Videocraft10/Vid-USB-Hub/Promo Files/Exports/BackgroundExport.png

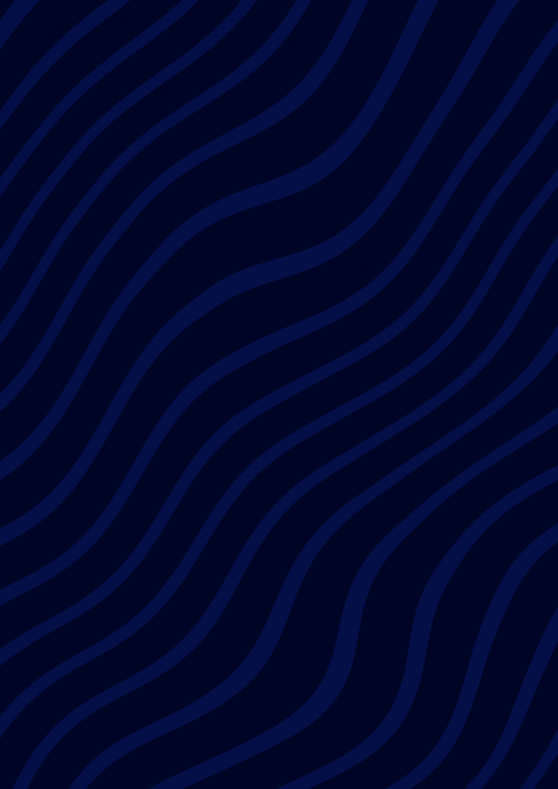
Promo Files/Exports/BackgroundExport.png
