Videocraft10/Vid-USB-Hub/Promo Files/Exports/BackgroundExportBland.png

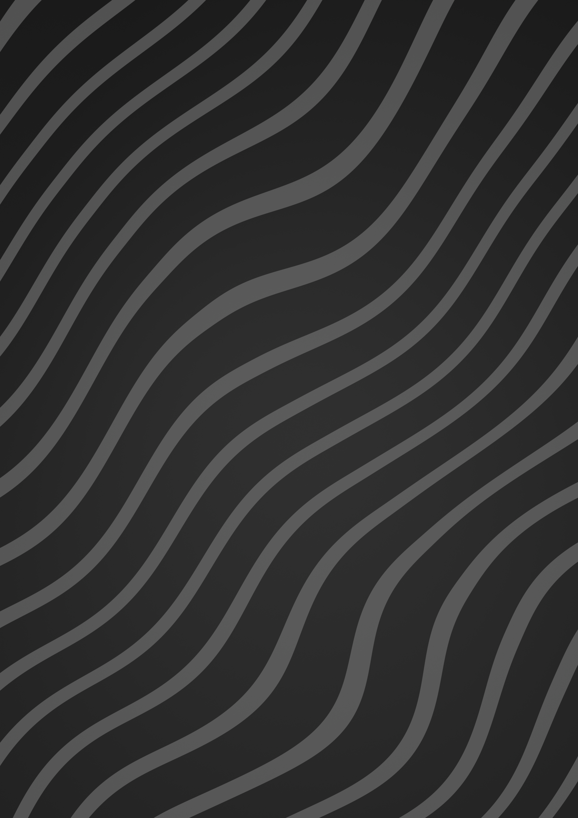
Promo Files/Exports/BackgroundExportBland.png
