Videocraft10/Vid-USB-Hub/Promo Files/Exports/BackgroundExportGlow.png

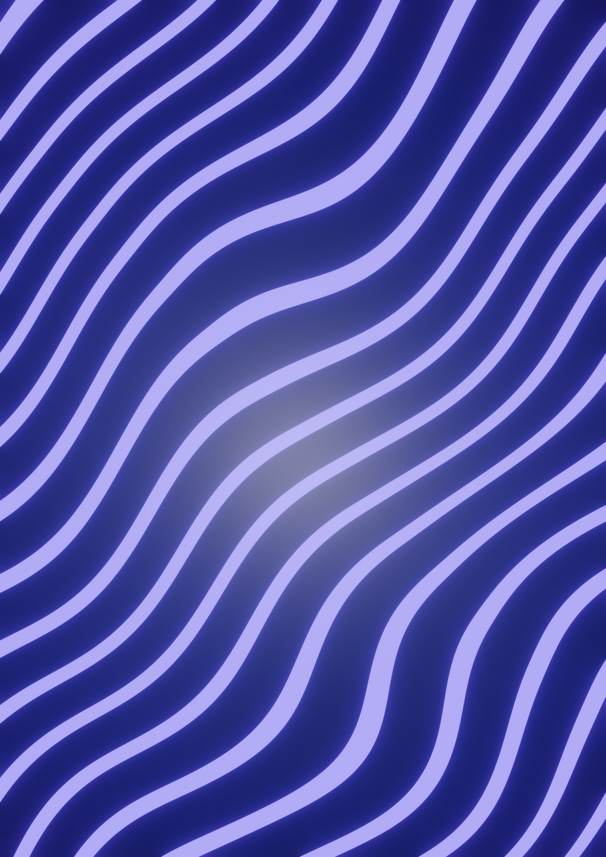
Promo Files/Exports/BackgroundExportGlow.png
