Videocraft10/Vid-USB-Hub/Promo Files/Exports/GitHubQR.png

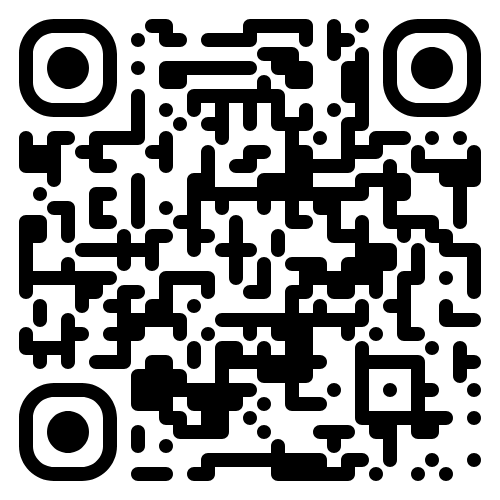
Promo Files/Exports/GitHubQR.png
