Videocraft10/Vid-USB-Hub/Promo Files/Exports/USB Grafiti Flip.png

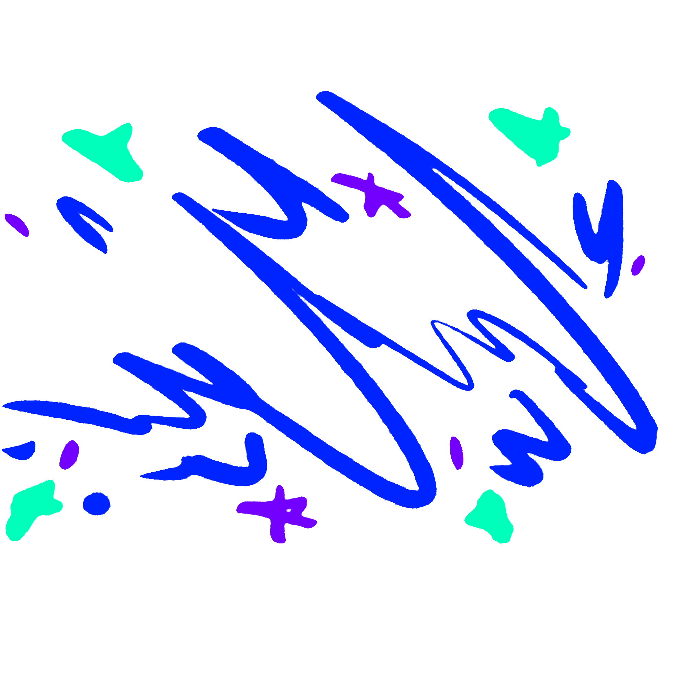
Promo Files/Exports/USB Grafiti Flip.png
