Videocraft10/Vid-USB-Hub/Promo Files/Exports/USB Grafiti Zinev2 flip.png

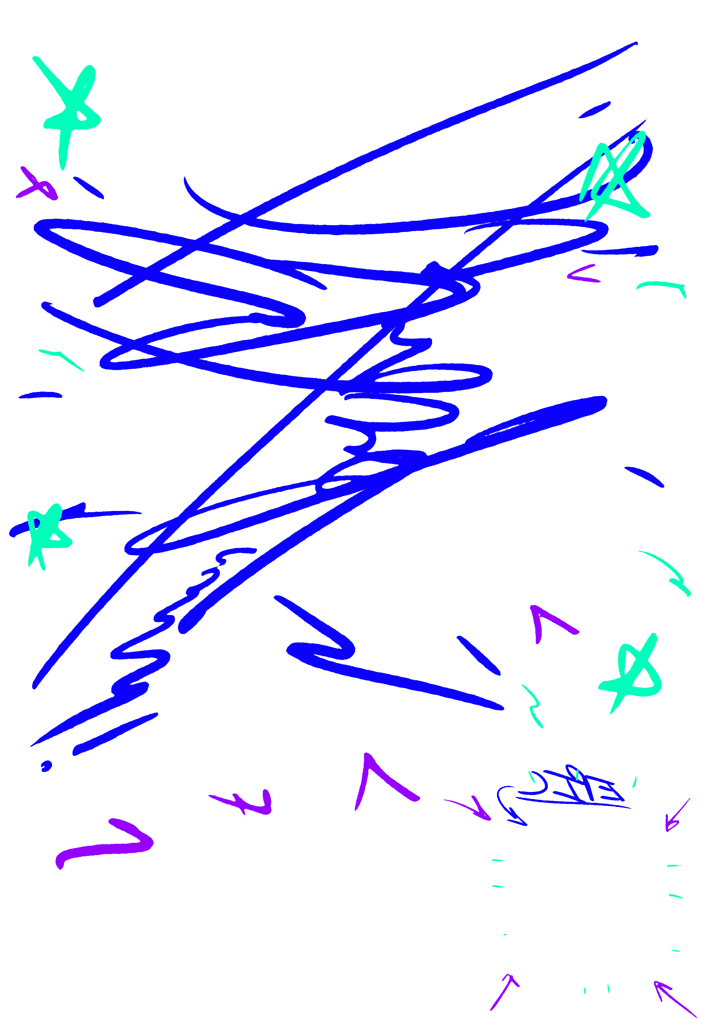
Promo Files/Exports/USB Grafiti Zinev2 flip.png
