Videocraft10/Vid-USB-Hub/Promo Files/Exports/USB Grafiti Zinev2.png

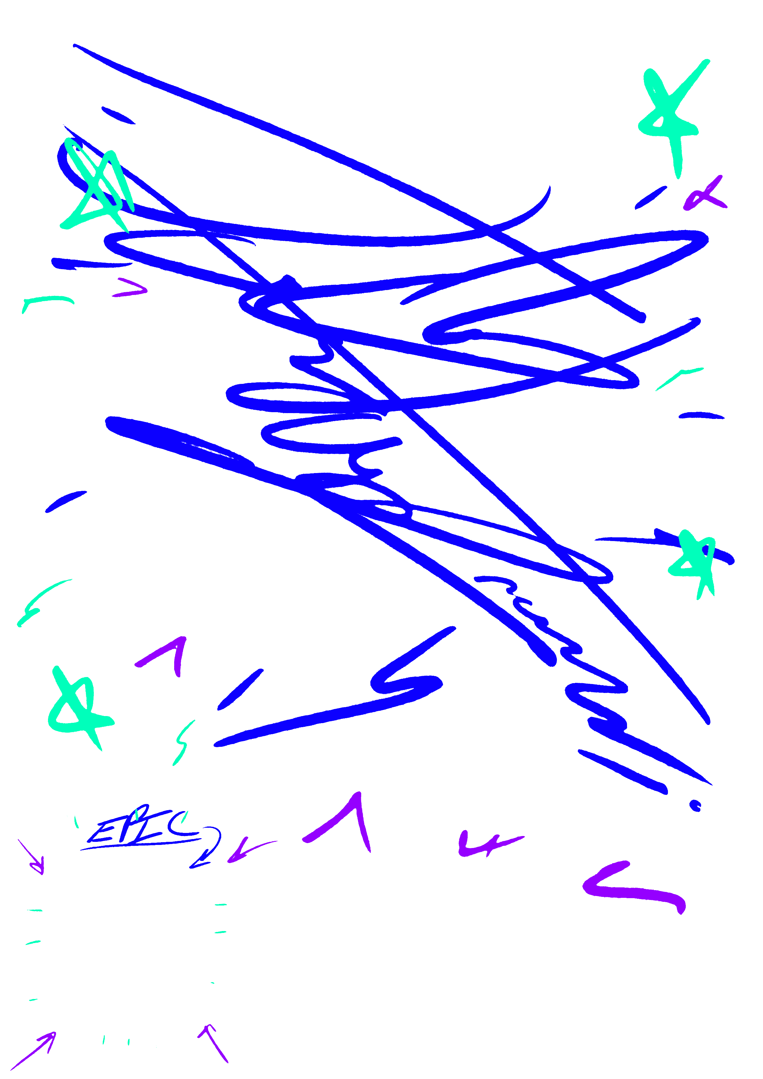
Promo Files/Exports/USB Grafiti Zinev2.png
