Videocraft10/Vid-USB-Hub/Promo Files/Exports/USB Grafiti.png

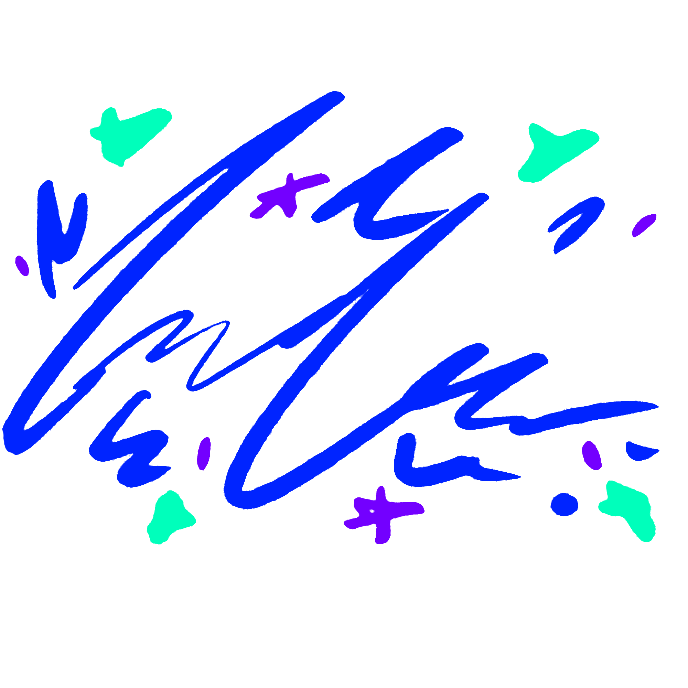
Promo Files/Exports/USB Grafiti.png
