Videocraft10/Vid-USB-Hub/Promo Files/Exports/USB Hub Main v2.png

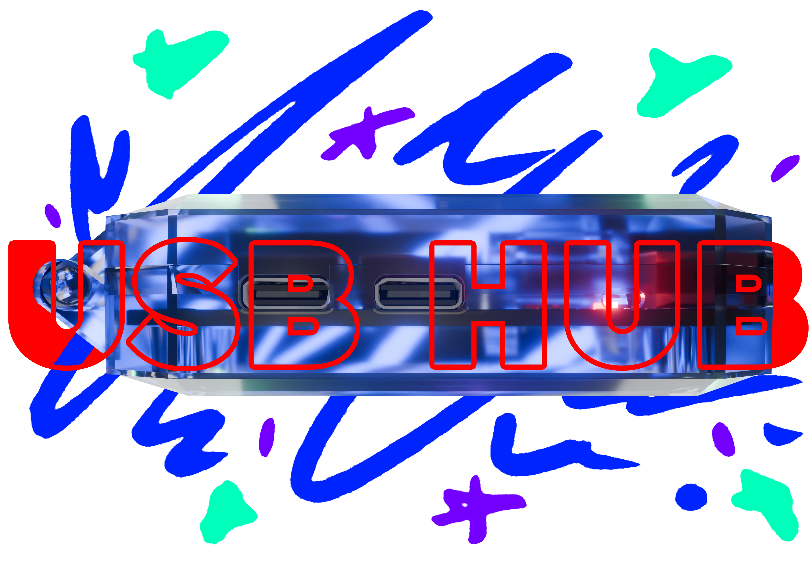
Promo Files/Exports/USB Hub Main v2.png
