Videocraft10/Vid-USB-Hub/Promo Files/Exports/USB Hub Main.png

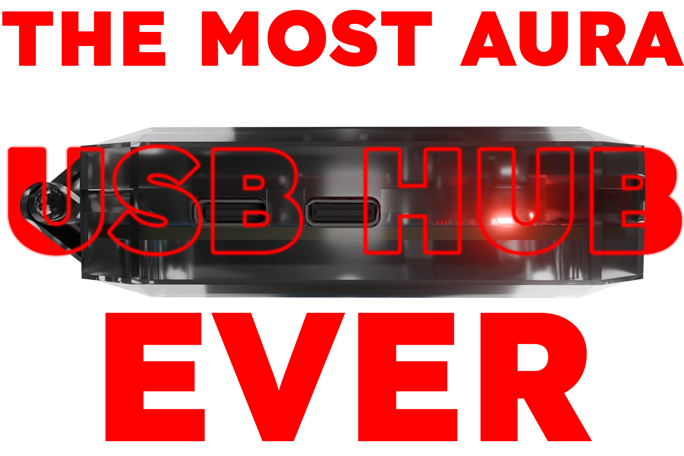
Promo Files/Exports/USB Hub Main.png
