Videocraft10/Vid-USB-Hub/Promo Files/Exports/USB Zine Empty 4 View.png

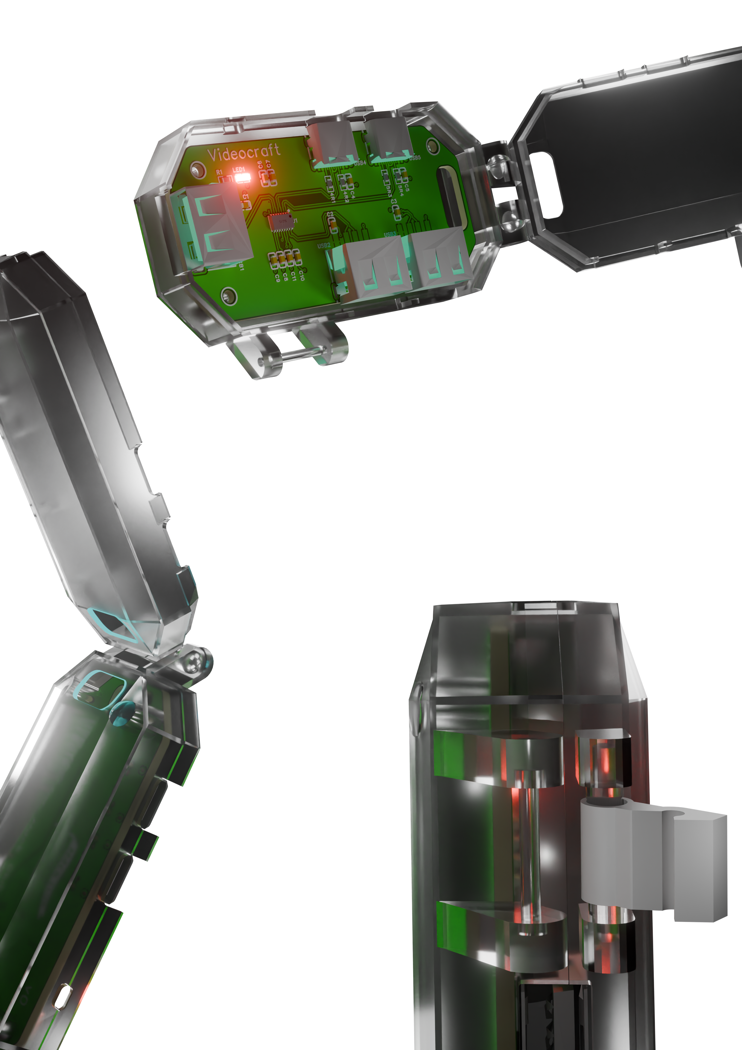
Promo Files/Exports/USB Zine Empty 4 View.png
