Videocraft10/Vid-USB-Hub/Promo Files/Exports/USB Zine Empty Side.png

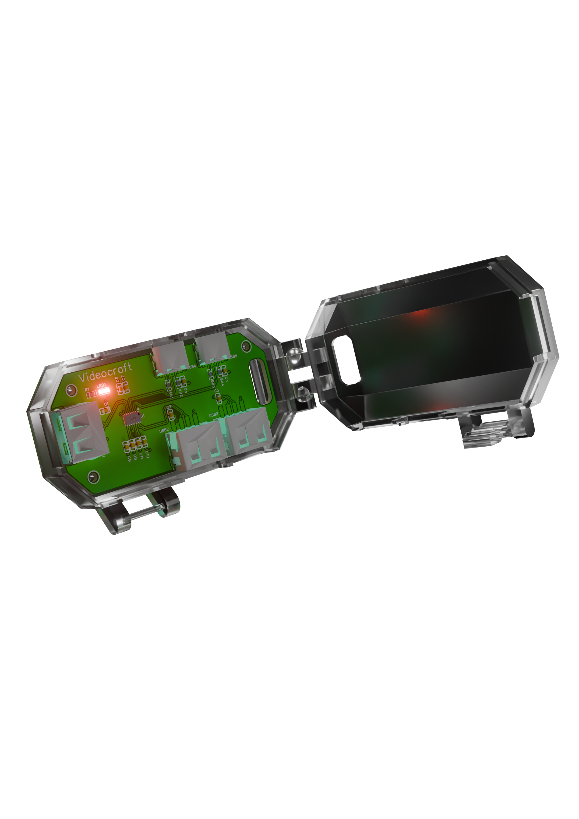
Promo Files/Exports/USB Zine Empty Side.png
