Videocraft10/Vid-USB-Hub/Promo Files/Exports/USB Zinev2 5 View With Update Art.png

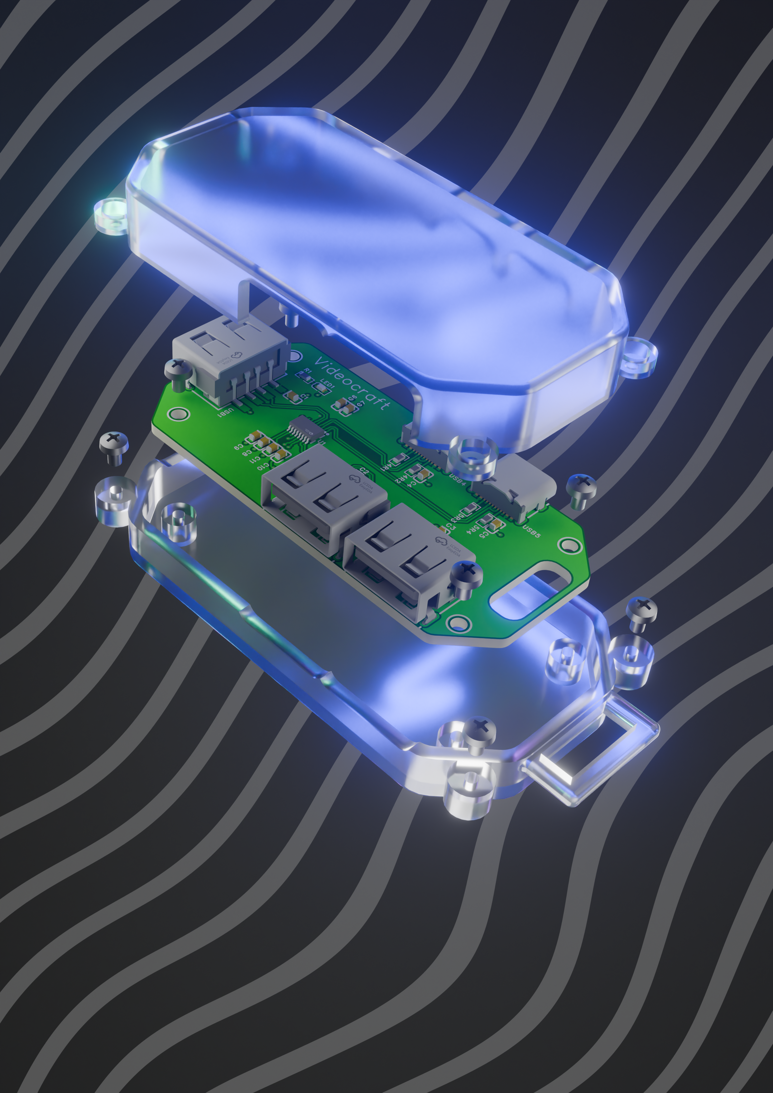
Promo Files/Exports/USB Zinev2 5 View With Update Art.png
