Videocraft10/Vid-USB-Hub/Promo Files/Exports/Videocraft USB Hub CAD Pic2.png

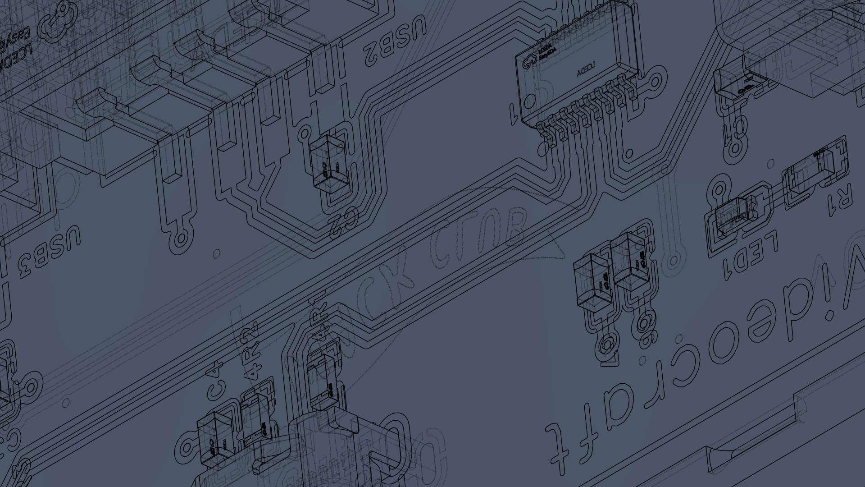
Promo Files/Exports/Videocraft USB Hub CAD Pic2.png
