Videocraft10/Vid-USB-Hub/Promo Files/Exports/Videocraft USB Hub v2 Zine v5 IRL.png

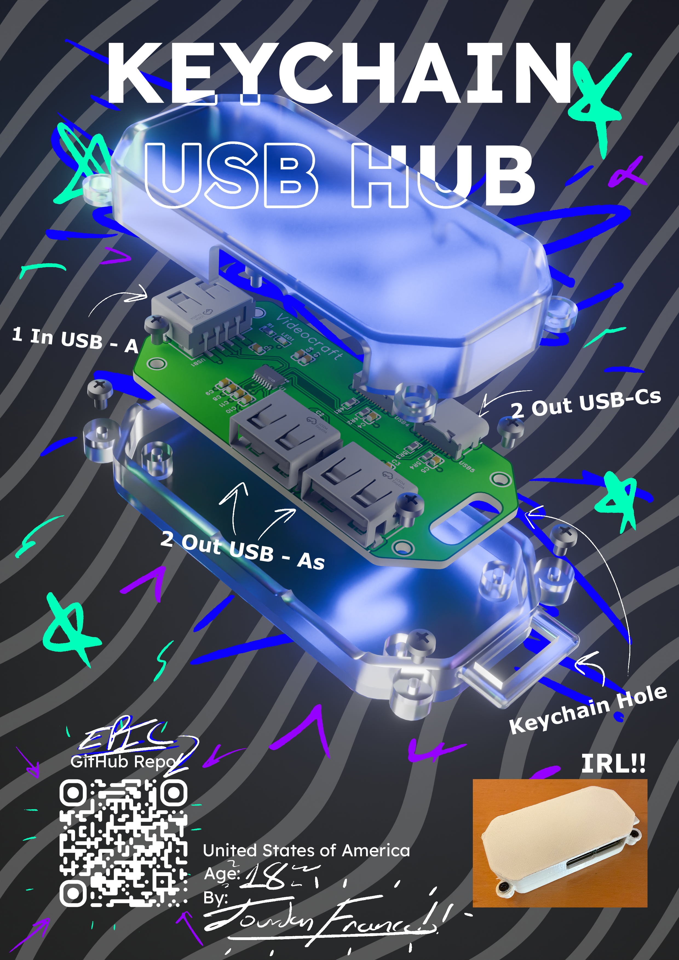
Promo Files/Exports/Videocraft USB Hub v2 Zine v5 IRL.png
