Videocraft10/Vid-USB-Hub/Promo Files/Exports/Videocraft USB Hub Zine v4.png

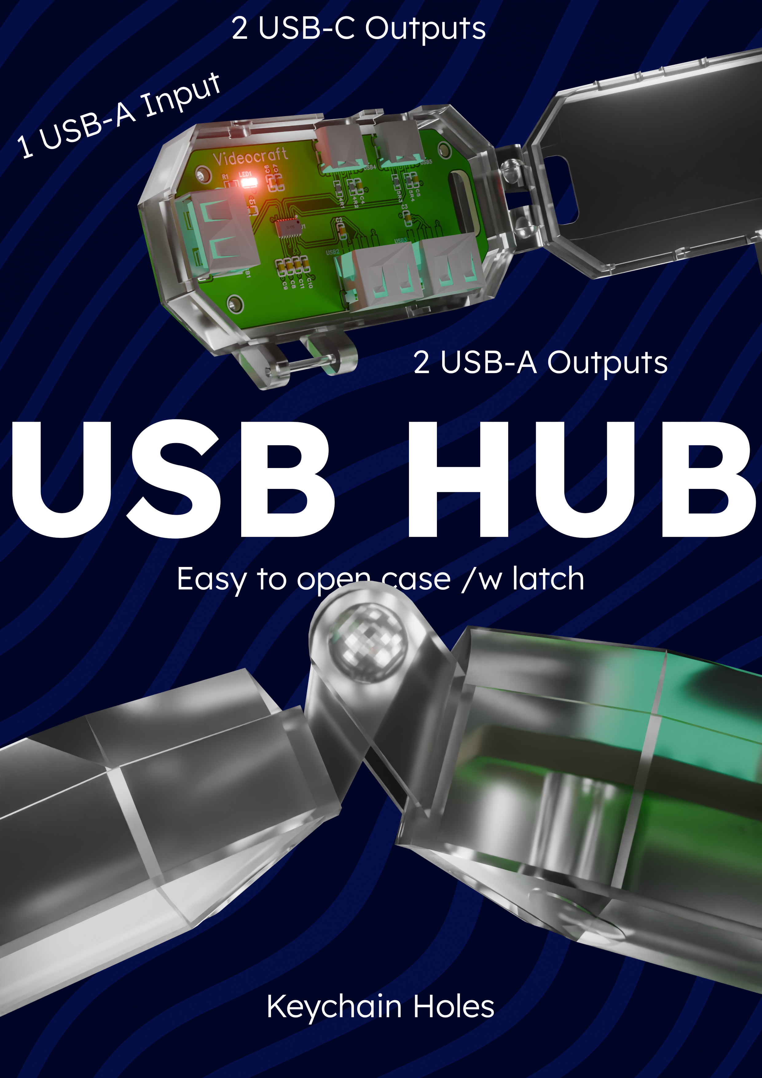
Promo Files/Exports/Videocraft USB Hub Zine v4.png
